ashep/cronus/src/main/bt.c

#include "cronus/bt.h"
#include "cronus/cfg.h"
#include "cronus/display.h"
#include <string.h>
#include "esp_log.h"
#include "esp_event.h"
#include "dy/error.h"
#include "dy/bt.h"
#include "dy/appinfo.h"
#include "dy/cfg2.h"
#include "dy/cloud.h"

#define LTAG "CRONUS_BT"

typedef enum {
    CRONUS_BT_CHRC_TYPE_UINT8,
    CRONUS_BT_CHRC_TYPE_FLOAT,
    CRONUS_BT_CHRC_TYPE_STRING,
} cronus_bt_chrc_type_t;

static void on_bt_ready(void *arg, esp_event_base_t base, int32_t id, void *data) {
    dy_bt_evt_ready_t *evt = (dy_bt_evt_ready_t *) data;

    char addr[13];
    snprintf(addr, 13, "%02x%02x%02x%02x%02x%02x",
             evt->address[0], evt->address[1], evt->address[2], evt->address[3], evt->address[4], evt->address[5]);

    dy_appinfo_set_auth(addr);
}

static dy_err_t bt_chrc_uuid_to_cfg_id(cronus_bt_chrc_type_t type, esp_bt_uuid_t uuid, int *cfg_id) {
    if (type == CRONUS_BT_CHRC_TYPE_UINT8) {
        switch (uuid.uuid.uuid16) {
            case CRONUS_BT_CHRC_UUID_SHOW_MODE:
                *cfg_id = CRONUS_CFG_ID_SHOW_MODE;
                break;
            case CRONUS_BT_CHRC_UUID_BRIGHTNESS_MIN:
                *cfg_id = CRONUS_CFG_ID_BRIGHTNESS_MIN;
                break;
            case CRONUS_BT_CHRC_UUID_BRIGHTNESS_MAX:
                *cfg_id = CRONUS_CFG_ID_BRIGHTNESS_MAX;
                break;
            case CRONUS_BT_CHRC_UUID_SHOW_DUR_TIME:
                *cfg_id = CRONUS_CFG_ID_WIDGET_TIME_DURATION;
                break;
            case CRONUS_BT_CHRC_UUID_SHOW_DUR_DATE:
                *cfg_id = CRONUS_CFG_ID_WIDGET_DATE_DURATION;
                break;
            case CRONUS_BT_CHRC_UUID_SHOW_DUR_DOW:
                *cfg_id = CRONUS_CFG_ID_WIDGET_DOW_DURATION;
                break;
            case CRONUS_BT_CHRC_UUID_SHOW_DUR_AMB_TEMP:
                *cfg_id = CRONUS_CFG_ID_WIDGET_AMB_TEMP_DURATION;
                break;
            case CRONUS_BT_CHRC_UUID_SHOW_DUR_ODR_TEMP:
                *cfg_id = CRONUS_CFG_ID_WIDGET_ODR_TEMP_DURATION;
                break;
            case CRONUS_BT_CHRC_UUID_ALLOW_UNSTABLE_FIRMWARE:
                *cfg_id = CRONUS_CFG_ID_ALLOW_UNSTABLE_FW;
                break;
            case CRONUS_BT_CHRC_UUID_SHOW_DUR_WEATHER_ICON:
                *cfg_id = CRONUS_CFG_ID_WIDGET_WEATHER_DURATION;
                break;
            case CRONUS_BT_CHRC_UUID_LOCATION_NAME:
                *cfg_id = CRONUS_CFG_ID_LOCATION_NAME;
                break;
            case CRONUS_BT_CHRC_UUID_WIDGET_TIME_COLOR:
                *cfg_id = CRONUS_CFG_ID_WIDGET_TIME_COLOR;
                break;
            case CRONUS_BT_CHRC_UUID_WIDGET_DATE_COLOR:
                *cfg_id = CRONUS_CFG_ID_WIDGET_DATE_COLOR;
                break;
            case CRONUS_BT_CHRC_UUID_WIDGET_DOW_COLOR:
                *cfg_id = CRONUS_CFG_ID_WIDGET_DOW_COLOR;
                break;
            case CRONUS_BT_CHRC_UUID_WIDGET_AMB_TEMP_COLOR:
                *cfg_id = CRONUS_CFG_ID_WIDGET_AMB_TEMP_COLOR;
                break;
            case CRONUS_BT_CHRC_UUID_WIDGET_ODR_TEMP_COLOR:
                *cfg_id = CRONUS_CFG_ID_WIDGET_ODR_TEMP_COLOR;
                break;
            case CRONUS_BT_CHRC_UUID_NIGHT_MODE_ENABLED:
                *cfg_id = CRONUS_CFG_ID_NIGHT_MODE_ENABLED;
                break;
            case CRONUS_BT_CHRC_UUID_NIGHT_MODE_COLOR:
                *cfg_id = CRONUS_CFG_ID_NIGHT_MODE_COLOR;
                break;
            case CRONUS_BT_CHRC_UUID_SHOW_DUR_AIR_RAID_ALERT:
                *cfg_id = CRONUS_CFG_ID_WIDGET_DUR_AIR_RAID_ALERT;
                break;
            default:
                return dy_err(DY_ERR_INVALID_ARG, "unexpected characteristic uuid: 0x%04x", uuid.uuid.uuid16);
        }
    }

    if (type == CRONUS_BT_CHRC_TYPE_FLOAT) {
        switch (uuid.uuid.uuid16) {
            case CRONUS_BT_CHRC_UUID_LOCATION_LAT:
                *cfg_id = CRONUS_CFG_ID_LOCATION_LAT;
                break;
            case CRONUS_BT_CHRC_UUID_LOCATION_LNG:
                *cfg_id = CRONUS_CFG_ID_LOCATION_LNG;
                break;
            default:
                return dy_err(DY_ERR_INVALID_ARG, "unexpected characteristic uuid: 0x%04x", uuid.uuid.uuid16);
        }
    }

    if (type == CRONUS_BT_CHRC_TYPE_STRING) {
        switch (uuid.uuid.uuid16) {
            case CRONUS_BT_CHRC_UUID_LOCATION_NAME:
                *cfg_id = CRONUS_CFG_ID_LOCATION_NAME;
                break;
            default:
                return dy_err(DY_ERR_INVALID_ARG, "unexpected characteristic uuid: 0x%04x", uuid.uuid.uuid16);
        }
    }

    return dy_ok();
}

static dy_err_t on_uint8_const_read(esp_bt_uuid_t uuid, uint8_t *val, size_t *len) {
    *len = sizeof(uint8_t);

    switch (uuid.uuid.uuid16) {
        case CRONUS_BT_CHRC_UUID_DISPLAY_0_TYPE:
#ifdef CONFIG_CRONUS_DISPLAY_0_DRIVER_MAX7219_32X16
            *val = CRONUS_DISPLAY_TYPE_MAX7219_32X16;
#elifdef CONFIG_CRONUS_DISPLAY_0_DRIVER_WS2812_32X16
            *val = CRONUS_DISPLAY_TYPE_WS2812_32X16;
#else
            *val = CRONUS_DISPLAY_TYPE_NONE;
#endif
            break;
        default:
            return dy_err(DY_ERR_INVALID_ARG, "unexpected characteristic uuid: 0x%04x", uuid.uuid.uuid16);
    }

    return dy_ok();
}

static dy_err_t on_str_const_read(esp_bt_uuid_t uuid, uint8_t *val, size_t *len) {
    switch (uuid.uuid.uuid16) {
        case CRONUS_BT_CHRC_UUID_FIRMWARE_VERSION:
            *len = strlen(APP_VERSION);
            strlcpy((char *) val, APP_VERSION, DY_CFG2_STR_MAX_LEN);
            break;
        default:
            return dy_err(DY_ERR_INVALID_ARG, "unexpected characteristic uuid: 0x%04x", uuid.uuid.uuid16);
    }

    return dy_ok();
}

static dy_err_t on_uint8_read(esp_bt_uuid_t uuid, uint8_t *val, size_t *len) {
    dy_err_t err;
    int cfg_id = 0;

    if (dy_is_err(err = bt_chrc_uuid_to_cfg_id(CRONUS_BT_CHRC_TYPE_UINT8, uuid, &cfg_id))) {
        return err;
    }

    if (dy_is_err(err = dy_cfg2_get_u8_dft(cfg_id, (uint8_t *) val, 0))) {
        ESP_LOGW(LTAG, "dy_cfg2_get_u8 failed: %s", dy_err_str(err));
        return err;
    }

    *len = sizeof(uint8_t);

    return dy_ok();
}

static dy_err_t on_uint8_write(esp_bt_uuid_t uuid, const uint8_t *val, size_t len) {
    dy_err_t err;
    int cfg_id = 0;

    if (dy_is_err(err = bt_chrc_uuid_to_cfg_id(CRONUS_BT_CHRC_TYPE_UINT8, uuid, &cfg_id))) {
        return err;
    }

    if (dy_is_err(err = dy_cfg2_set_u8(cfg_id, *val))) {
        return err;
    }

    if (cfg_id == CRONUS_CFG_ID_WIDGET_DUR_AIR_RAID_ALERT) {
        dy_cloud_air_raid_alert_set_enabled(*val > 0);
    }

    return dy_ok();
}

static dy_err_t on_float_read(esp_bt_uuid_t uuid, uint8_t *val, size_t *len) {
    dy_err_t err;
    int cfg_id = 0;
    float value = 0;

    if (dy_is_err(err = bt_chrc_uuid_to_cfg_id(CRONUS_BT_CHRC_TYPE_FLOAT, uuid, &cfg_id))) {
        return err;
    }

    if (dy_is_err(err = dy_cfg2_get_float_dft(cfg_id, &value, 0))) {
        ESP_LOGW(LTAG, "dy_cfg2_get_float failed: %s", dy_err_str(err));
        return err;
    }

    memcpy(val, &value, sizeof(float));
    *len = sizeof(float);

    return dy_ok();
}

static dy_err_t on_float_write(esp_bt_uuid_t uuid, const uint8_t *val, size_t len) {
    dy_err_t err;
    int cfg_id = 0;
    float value = 0;

    if (dy_is_err(err = bt_chrc_uuid_to_cfg_id(CRONUS_BT_CHRC_TYPE_FLOAT, uuid, &cfg_id))) {
        return err;
    }

    memcpy(&value, val, sizeof(float));
    if (dy_is_err(err = dy_cfg2_set_float(cfg_id, value))) {
        return err;
    }

    switch (cfg_id) {
        case CRONUS_CFG_ID_LOCATION_LAT:
            dy_cloud_set_location_lat(value);
            break;
        case CRONUS_CFG_ID_LOCATION_LNG:
            dy_cloud_set_location_lng(value);
            break;
        default:
            break;
    }

    return dy_ok();
}

static dy_err_t on_string_read(esp_bt_uuid_t uuid, uint8_t *val, size_t *len) {
    dy_err_t err;
    int cfg_id = 0;

    if (dy_is_err(err = bt_chrc_uuid_to_cfg_id(CRONUS_BT_CHRC_TYPE_STRING, uuid, &cfg_id))) {
        return err;
    }

    if (dy_is_err(err = dy_cfg2_get_str_dft(cfg_id, (char *) val, ""))) {
        ESP_LOGW(LTAG, "dy_cfg2_get_str failed: %s", dy_err_str(err));
        return err;
    }

    *len = strlen((const char *) val);

    return dy_ok();
}

static dy_err_t on_string_write(esp_bt_uuid_t uuid, const uint8_t *val, size_t len) {
    dy_err_t err;
    int cfg_id = 0;

    len += 1; // for the null terminator

    if (dy_is_err(err = bt_chrc_uuid_to_cfg_id(CRONUS_BT_CHRC_TYPE_STRING, uuid, &cfg_id))) {
        return err;
    }

    if (len > DY_CFG2_STR_MAX_LEN) {
        return dy_err(DY_ERR_INVALID_ARG, "value is too long: %d", len);
    }

    char buf[DY_CFG2_STR_MAX_LEN];
    strlcpy(buf, (const char *) val, len);

    if (dy_is_err(err = dy_cfg2_set_str(cfg_id, (const char *) buf))) {
        return err;
    }

    return dy_ok();
}

dy_err_t cronus_bt_init() {
    esp_err_t esp_err;
    dy_err_t err;

    esp_err = esp_event_handler_register(DY_BT_EVENT_BASE, DY_BT_EVENT_READY, on_bt_ready, NULL);
    if (esp_err != ESP_OK) {
        return dy_err(DY_ERR_FAILED, "esp_event_handler_register: %s", esp_err_to_name(esp_err));
    }

    if (dy_is_err(err = dy_bt_set_device_name_prefix("Cronus"))) {
        return dy_err_pfx("dy_bt_set_device_name_prefix", err);
    }

    if (dy_is_err(err = dy_bt_set_device_appearance(0x0100))) {
        // Generic Clock
        return dy_err_pfx("dy_bt_set_device_appearance", err);
    }

    err = dy_bt_register_characteristic(CRONUS_BT_CHRC_UUID_FIRMWARE_VERSION, on_str_const_read, NULL);
    if (dy_is_err(err)) {
        return dy_err_pfx("dy_bt_register_characteristic: FIRMWARE_VERSION", err);
    }

    err = dy_bt_register_characteristic(CRONUS_BT_CHRC_UUID_DISPLAY_0_TYPE, on_uint8_const_read, NULL);
    if (dy_is_err(err)) {
        return dy_err_pfx("dy_bt_register_characteristic: DISPLAY_0_TYPE", err);
    }

    err = dy_bt_register_characteristic(CRONUS_BT_CHRC_UUID_SHOW_MODE, on_uint8_read, on_uint8_write);
    if (dy_is_err(err)) {
        return dy_err_pfx("dy_bt_register_characteristic: SHOW_MODE", err);
    }

    err = dy_bt_register_characteristic(CRONUS_BT_CHRC_UUID_BRIGHTNESS_MIN, on_uint8_read, on_uint8_write);
    if (dy_is_err(err)) {
        return dy_err_pfx("dy_bt_register_characteristic: BRIGHTNESS_MIN", err);
    }

    err = dy_bt_register_characteristic(CRONUS_BT_CHRC_UUID_BRIGHTNESS_MAX, on_uint8_read, on_uint8_write);
    if (dy_is_err(err)) {
        return dy_err_pfx("dy_bt_register_characteristic: BRIGHTNESS_MAX", err);
    }

    err = dy_bt_register_characteristic(CRONUS_BT_CHRC_UUID_SHOW_DUR_TIME, on_uint8_read, on_uint8_write);
    if (dy_is_err(err)) {
        return dy_err_pfx("dy_bt_register_characteristic: SHOW_DUR_TIME", err);
    }

    err = dy_bt_register_characteristic(CRONUS_BT_CHRC_UUID_SHOW_DUR_DATE, on_uint8_read, on_uint8_write);
    if (dy_is_err(err)) {
        return dy_err_pfx("dy_bt_register_characteristic: SHOW_DUR_DATE", err);
    }

    err = dy_bt_register_characteristic(CRONUS_BT_CHRC_UUID_SHOW_DUR_DOW, on_uint8_read, on_uint8_write);
    if (dy_is_err(err)) {
        return dy_err_pfx("dy_bt_register_characteristic: SHOW_DUR_DOW", err);
    }

    err = dy_bt_register_characteristic(CRONUS_BT_CHRC_UUID_SHOW_DUR_AMB_TEMP, on_uint8_read, on_uint8_write);
    if (dy_is_err(err)) {
        return dy_err_pfx("dy_bt_register_characteristic: SHOW_DUR_AMB_TEMP", err);
    }

    err = dy_bt_register_characteristic(CRONUS_BT_CHRC_UUID_SHOW_DUR_ODR_TEMP, on_uint8_read, on_uint8_write);
    if (dy_is_err(err)) {
        return dy_err_pfx("dy_bt_register_characteristic: SHOW_DUR_ODR_TEMP", err);
    }

    err = dy_bt_register_characteristic(CRONUS_BT_CHRC_UUID_ALLOW_UNSTABLE_FIRMWARE, on_uint8_read, on_uint8_write);
    if (dy_is_err(err)) {
        return dy_err_pfx("dy_bt_register_characteristic: ALLOW_UNSTABLE_FIRMWARE", err);
    }

    err = dy_bt_register_characteristic(CRONUS_BT_CHRC_UUID_SHOW_DUR_WEATHER_ICON, on_uint8_read, on_uint8_write);
    if (dy_is_err(err)) {
        return dy_err_pfx("dy_bt_register_characteristic: SHOW_DUR_WEATHER_ICON", err);
    }

    err = dy_bt_register_characteristic(CRONUS_BT_CHRC_UUID_LOCATION_NAME, on_string_read, on_string_write);
    if (dy_is_err(err)) {
        return dy_err_pfx("dy_bt_register_characteristic: LOCATION_NAME", err);
    }

    err = dy_bt_register_characteristic(CRONUS_BT_CHRC_UUID_LOCATION_LAT, on_float_read, on_float_write);
    if (dy_is_err(err)) {
        return dy_err_pfx("dy_bt_register_characteristic: LOCATION_LAT", err);
    }

    err = dy_bt_register_characteristic(CRONUS_BT_CHRC_UUID_LOCATION_LNG, on_float_read, on_float_write);
    if (dy_is_err(err)) {
        return dy_err_pfx("dy_bt_register_characteristic: LOCATION_LNG", err);
    }

    err = dy_bt_register_characteristic(CRONUS_BT_CHRC_UUID_WIDGET_TIME_COLOR, on_uint8_read, on_uint8_write);
    if (dy_is_err(err)) {
        return dy_err_pfx("dy_bt_register_characteristic: WIDGET_TIME_COLOR", err);
    }

    err = dy_bt_register_characteristic(CRONUS_BT_CHRC_UUID_WIDGET_DATE_COLOR, on_uint8_read, on_uint8_write);
    if (dy_is_err(err)) {
        return dy_err_pfx("dy_bt_register_characteristic: WIDGET_DATE_COLOR", err);
    }

    err = dy_bt_register_characteristic(CRONUS_BT_CHRC_UUID_WIDGET_DOW_COLOR, on_uint8_read, on_uint8_write);
    if (dy_is_err(err)) {
        return dy_err_pfx("dy_bt_register_characteristic: WIDGET_DOW_COLOR", err);
    }

    err = dy_bt_register_characteristic(CRONUS_BT_CHRC_UUID_WIDGET_AMB_TEMP_COLOR, on_uint8_read, on_uint8_write);
    if (dy_is_err(err)) {
        return dy_err_pfx("dy_bt_register_characteristic: WIDGET_AMB_TEMP_COLOR", err);
    }

    err = dy_bt_register_characteristic(CRONUS_BT_CHRC_UUID_WIDGET_ODR_TEMP_COLOR, on_uint8_read, on_uint8_write);
    if (dy_is_err(err)) {
        return dy_err_pfx("dy_bt_register_characteristic: WIDGET_ODR_TEMP_COLOR", err);
    }

    err = dy_bt_register_characteristic(CRONUS_BT_CHRC_UUID_NIGHT_MODE_ENABLED, on_uint8_read, on_uint8_write);
    if (dy_is_err(err)) {
        return dy_err_pfx("dy_bt_register_characteristic: NIGHT_MODE_ENABLED", err);
    }

    err = dy_bt_register_characteristic(CRONUS_BT_CHRC_UUID_NIGHT_MODE_COLOR, on_uint8_read, on_uint8_write);
    if (dy_is_err(err)) {
        return dy_err_pfx("dy_bt_register_characteristic: NIGHT_MODE_COLOR", err);
    }

    err = dy_bt_register_characteristic(CRONUS_BT_CHRC_UUID_SHOW_DUR_AIR_RAID_ALERT, on_uint8_read, on_uint8_write);
    if (dy_is_err(err)) {
        return dy_err_pfx("dy_bt_register_characteristic: SHOW_DUR_AIR_RAID_ALERT", err);
    }

    if (dy_is_err(err = dy_bt_init())) {
        return dy_err_pfx("dy_bt_init", err);
    }

    return dy_ok();
}
