ashep/cronus/src/main/cfg.c

#include "cronus/cfg.h"
#include "cronus/screen.h"
#include "esp_log.h"
#include "dy/error.h"
#include "dy/cfg2.h"
#include "dy/gfx/gfx.h"

#define LTAG "MAIN"

static void set_u8_if_not_set(int id, uint8_t val) {
    if (dy_cfg2_is_set(id)) {
        return;
    }
    dy_err_t err = dy_cfg2_set_u8(id, val);
    if (dy_is_err(err)) {
        ESP_LOGW(LTAG, "dy_cfg2_set_u8 failed: %s", dy_err_str(err));
    } else {
        ESP_LOGW(LTAG, "default config value set: %d=%d", id, val);
    }
}

static void set_float_if_not_set(int id, float val) {
    if (dy_cfg2_is_set(id)) {
        return;
    }
    dy_err_t err = dy_cfg2_set_float(id, val);
    if (dy_is_err(err)) {
        ESP_LOGW(LTAG, "dy_cfg2_set_float failed: %s", dy_err_str(err));
    } else {
        ESP_LOGW(LTAG, "default config value set: %d=%f", id, val);
    }
}

static void set_str_if_not_set(int id, const char *val) {
    if (dy_cfg2_is_set(id)) {
        return;
    }
    dy_err_t err = dy_cfg2_set_str(id, val);
    if (dy_is_err(err)) {
        ESP_LOGW(LTAG, "dy_cfg2_set_str failed: %s", dy_err_str(err));
    } else {
        ESP_LOGW(LTAG, "default config value set: %d='%s'", id, val);
    }
}

static void set_config_defaults() {
    set_u8_if_not_set(CRONUS_CFG_ID_SHOW_MODE, CRONUS_CFG_USER_SHOW_MODE_SINGLE_LINE);
    set_u8_if_not_set(CRONUS_CFG_ID_BRIGHTNESS_MIN, 0);
    set_u8_if_not_set(CRONUS_CFG_ID_BRIGHTNESS_MAX, 15);
    set_u8_if_not_set(CRONUS_CFG_ID_WIDGET_TIME_DURATION, 5);
    set_u8_if_not_set(CRONUS_CFG_ID_WIDGET_DATE_DURATION, 2);
    set_u8_if_not_set(CRONUS_CFG_ID_WIDGET_DOW_DURATION, 0); // not implemented yet
    set_u8_if_not_set(CRONUS_CFG_ID_WIDGET_AMB_TEMP_DURATION, 0); // not implemented yet
    set_u8_if_not_set(CRONUS_CFG_ID_WIDGET_ODR_TEMP_DURATION, 2);
    set_u8_if_not_set(CRONUS_CFG_ID_ALLOW_UNSTABLE_FW, 0);
    set_u8_if_not_set(CRONUS_CFG_ID_WIDGET_WEATHER_DURATION, 2);
    set_str_if_not_set(CRONUS_CFG_ID_LOCATION_NAME, "");
    set_float_if_not_set(CRONUS_CFG_ID_LOCATION_LAT, 0);
    set_float_if_not_set(CRONUS_CFG_ID_LOCATION_LNG, 0);
    set_u8_if_not_set(CRONUS_CFG_ID_WIDGET_TIME_COLOR, DY_GFX_COLOR_GREEN);
    set_u8_if_not_set(CRONUS_CFG_ID_WIDGET_DATE_COLOR, DY_GFX_COLOR_GREEN);
    set_u8_if_not_set(CRONUS_CFG_ID_WIDGET_DOW_COLOR, DY_GFX_COLOR_GREEN);
    set_u8_if_not_set(CRONUS_CFG_ID_WIDGET_AMB_TEMP_COLOR, DY_GFX_COLOR_GREEN);
    set_u8_if_not_set(CRONUS_CFG_ID_WIDGET_ODR_TEMP_COLOR, DY_GFX_COLOR_GREEN);
    set_u8_if_not_set(CRONUS_CFG_ID_NIGHT_MODE_ENABLED, 1);
    set_u8_if_not_set(CRONUS_CFG_ID_NIGHT_MODE_COLOR, DY_GFX_COLOR_RED);
    set_u8_if_not_set(CRONUS_CFG_ID_WIDGET_DUR_AIR_RAID_ALERT, 0);
}

dy_err_t init_config() {
    dy_err_t err;

    if (dy_is_err(err = dy_cfg2_init())) {
        return dy_err_pfx("dy_cfg2_init", err);
    }

    set_config_defaults();

    // Prepare migration flag for future migrations
    uint8_t d;
    if (dy_is_err(err = dy_cfg2_get_u8_dft(CRONUS_CFG_MIGRATED, &d, 0))) {
        ESP_LOGE(LTAG, "get CRONUS_CFG_MIGRATED: %s", dy_err_str(err));
    } else if (d != 0) {
        if (dy_is_err(err = dy_cfg2_set_u8(CRONUS_CFG_MIGRATED, 0))) {
            ESP_LOGE(LTAG, "set CRONUS_CFG_MIGRATED: %s", dy_err_str(err));
        } else {
            ESP_LOGI(LTAG, "CRONUS_CFG_MIGRATED set to 0");
        }
    }

    return dy_ok();
}
