ashep/cronus/src/main/include/cronus/icon.h

#pragma once

#include "dy/gfx/sprite.h"

// Monochrome
extern const dy_gfx_sprite_t cronus_icon_m_cloudy;
extern const dy_gfx_sprite_t cronus_icon_m_partly_cloudy_day;
extern const dy_gfx_sprite_t cronus_icon_m_partly_cloudy_night;

// Colorful
extern const dy_gfx_sprite_t cronus_icon_c_cloudy;
extern const dy_gfx_sprite_t cronus_icon_c_partly_cloudy_day;
extern const dy_gfx_sprite_t cronus_icon_c_partly_cloudy_night;

// Universal
extern const dy_gfx_sprite_t cronus_icon_u_alert;
extern const dy_gfx_sprite_t cronus_icon_u_clear_day;
extern const dy_gfx_sprite_t cronus_icon_u_clear_night;
extern const dy_gfx_sprite_t cronus_icon_u_heavy_rain;
extern const dy_gfx_sprite_t cronus_icon_u_heavy_snow;
extern const dy_gfx_sprite_t cronus_icon_u_medium_rain;
extern const dy_gfx_sprite_t cronus_icon_u_medium_snow;
extern const dy_gfx_sprite_t cronus_icon_u_hourglass;
extern const dy_gfx_sprite_t cronus_icon_u_light_rain;
extern const dy_gfx_sprite_t cronus_icon_u_light_snow;
extern const dy_gfx_sprite_t cronus_icon_u_mist;
extern const dy_gfx_sprite_t cronus_icon_u_ok;
extern const dy_gfx_sprite_t cronus_icon_u_question;
extern const dy_gfx_sprite_t cronus_icon_u_thunderstorm;
