ashep/cronus/src/main/weather.c

#include <string.h>
#include <time.h>
#include "esp_log.h"
#include "esp_event.h"
#include "dy/error.h"
#include "dy/cloud.h"

#define LTAG "WEATHER"

static SemaphoreHandle_t mux;
static dy_cloud_weather_t weather;

static void weather_update_handler(void *arg, esp_event_base_t base, int32_t id, void *data) {
    const dy_cloud_weather_t *dt = data;

    if (xSemaphoreTake(mux, portTICK_PERIOD_MS) != pdTRUE) {
        ESP_LOGE(LTAG, "xSemaphoreTake failed");
        return;
    }

    strlcpy(weather.title, dt->title, DY_CLOUD_WEATHER_TITLE_LEN);
    weather.id = dt->id;
    weather.is_day = dt->is_day;
    weather.temp = dt->temp;
    weather.feels = dt->feels;
    weather.ts = dt->ts;

    xSemaphoreGive(mux);

    ESP_LOGI(LTAG, "weather updated");
}

dy_err_t cronus_weather_init() {
    dy_err_t err;

    mux = xSemaphoreCreateMutex();
    if (mux == NULL) {
        return dy_err(DY_ERR_NO_MEM, "xSemaphoreCreateMutex returned null");
    }

    if (dy_is_err(err = dy_cloud_weather_scheduler_start())) {
        return dy_err_pfx("dy_cloud_weather_scheduler_start", err);
    }

    const esp_err_t esp_err = esp_event_handler_register(
        DY_CLOUD_EV_BASE, DY_CLOUD_EV_WEATHER_UPDATED, weather_update_handler, NULL);
    if (esp_err != ESP_OK) {
        return dy_err(DY_ERR_FAILED, "esp_event_handler_register: %s", esp_err_to_name(esp_err));
    }

    return dy_ok();
}

dy_cloud_weather_t cronus_weather_get() {
    if (xSemaphoreTake(mux, portTICK_PERIOD_MS) != pdTRUE) {
        ESP_LOGE(LTAG, "xSemaphoreTake failed");
        return (dy_cloud_weather_t){0};
    }
    const dy_cloud_weather_t res = weather;
    xSemaphoreGive(mux);

    return res;
}

bool cronus_is_weather_obsolete() {
    if (xSemaphoreTake(mux, portTICK_PERIOD_MS) != pdTRUE) {
        ESP_LOGE(LTAG, "xSemaphoreTake failed");
        return 0;
    }
    const time_t age = time(NULL) - weather.ts;
    xSemaphoreGive(mux);

    return age <= 0 || age > 1800;
}
